NadavBenda/close-the-door-analog/LTspice_simulation/close_the_door_OS.asc

A1: and; Vhigh=5
A2: inv; Vhigh=5
C1: cap; 10n
C2: cap; 10µ
C4: cap; 10µ
C5: cap; 660p
C6: cap; 300n
C7: cap; 100µ
D1: diode; 1N4148
D2: diode; 1N4148
M1: nmos; 2N7002
R1: res; 10k
R2: res; 100
R3: res; 100k
R4: res; 100k
R5: res; 100k
R6: res; 500k
R7: res; 1k
R8: res; 1k
R11: res; 800k
R12: res; 200k
R13: res; {R+1k}
R14: res; {1meg+1k-R}
R18: res; 5k
R19: res; 1Meg
S1: sw
U1: LTC6993-3
U2: LTC6993-3
U3: NE555
U4: NE555
V1: voltage; 3
V2: voltage; PULSE(0 5 2 1m 1m 500)
Named nets: 0, VCC, sensor_sig, delay_os_out, beep_length_os_out, beep_periods, beeps, DIV
.tran 70
.model SW SW(Ron=1 Roff=1meg Vt=2.5)
TMP
buzzer
.param R 950k
.step param R 0 1meg 250k
